So11Deo6loria/bhvBadge2023/hardware/Badgetastic/Badgetastic.kicad_pcb

## KiCad design aqua_pcb/breakout_board.kicad_pcb

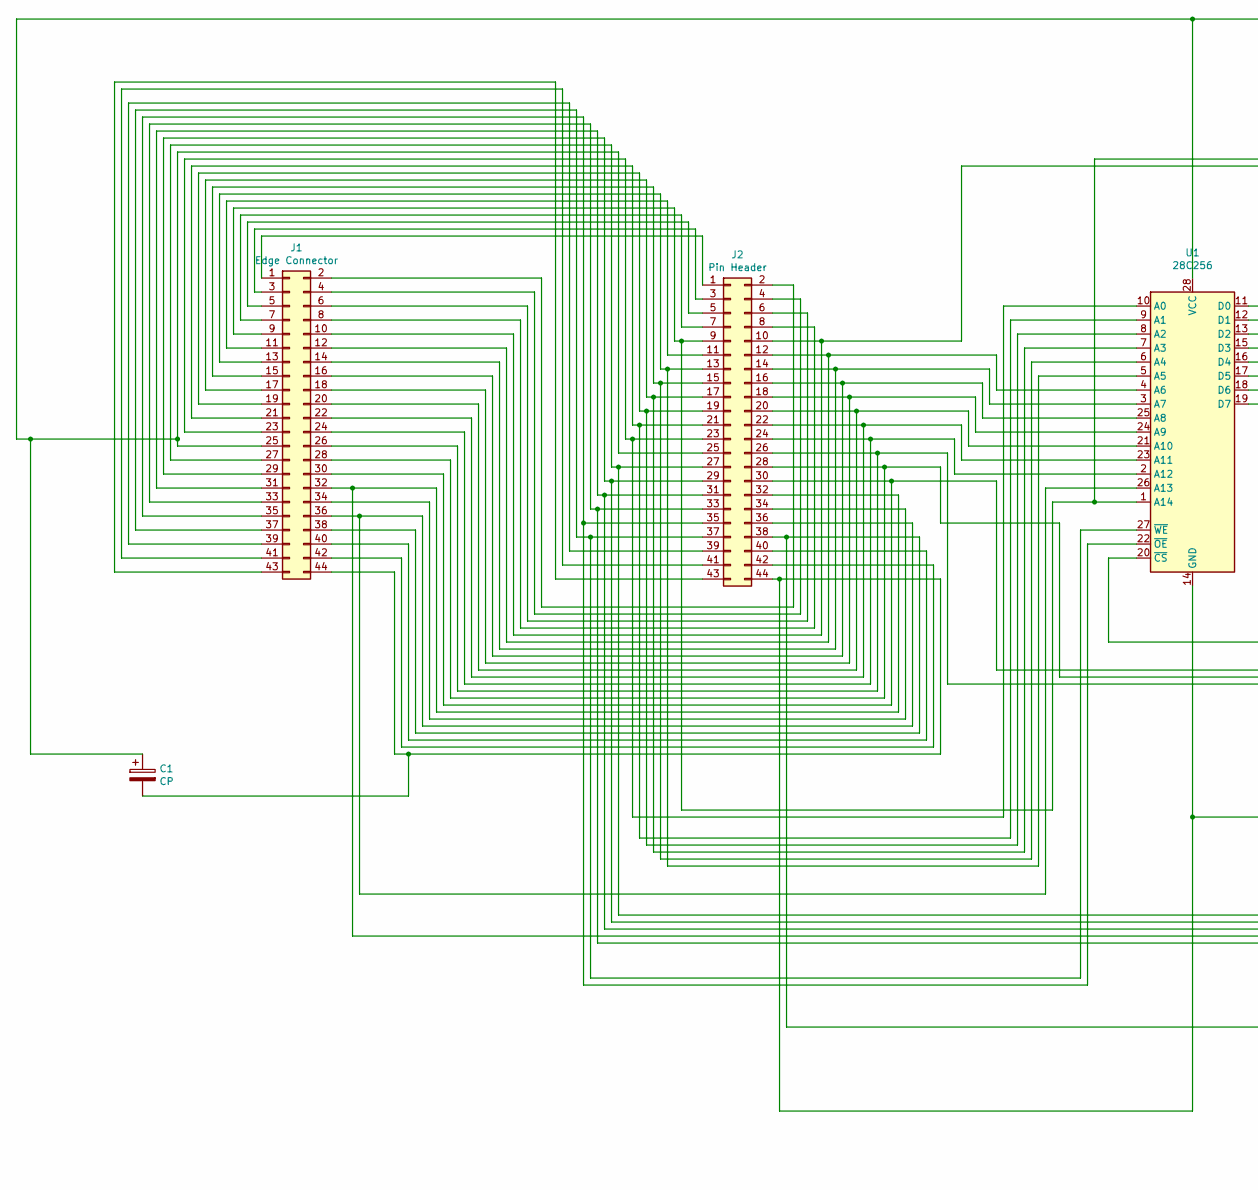
[picture p2: schematic breakout_board.sch, part in row 1, column 1]

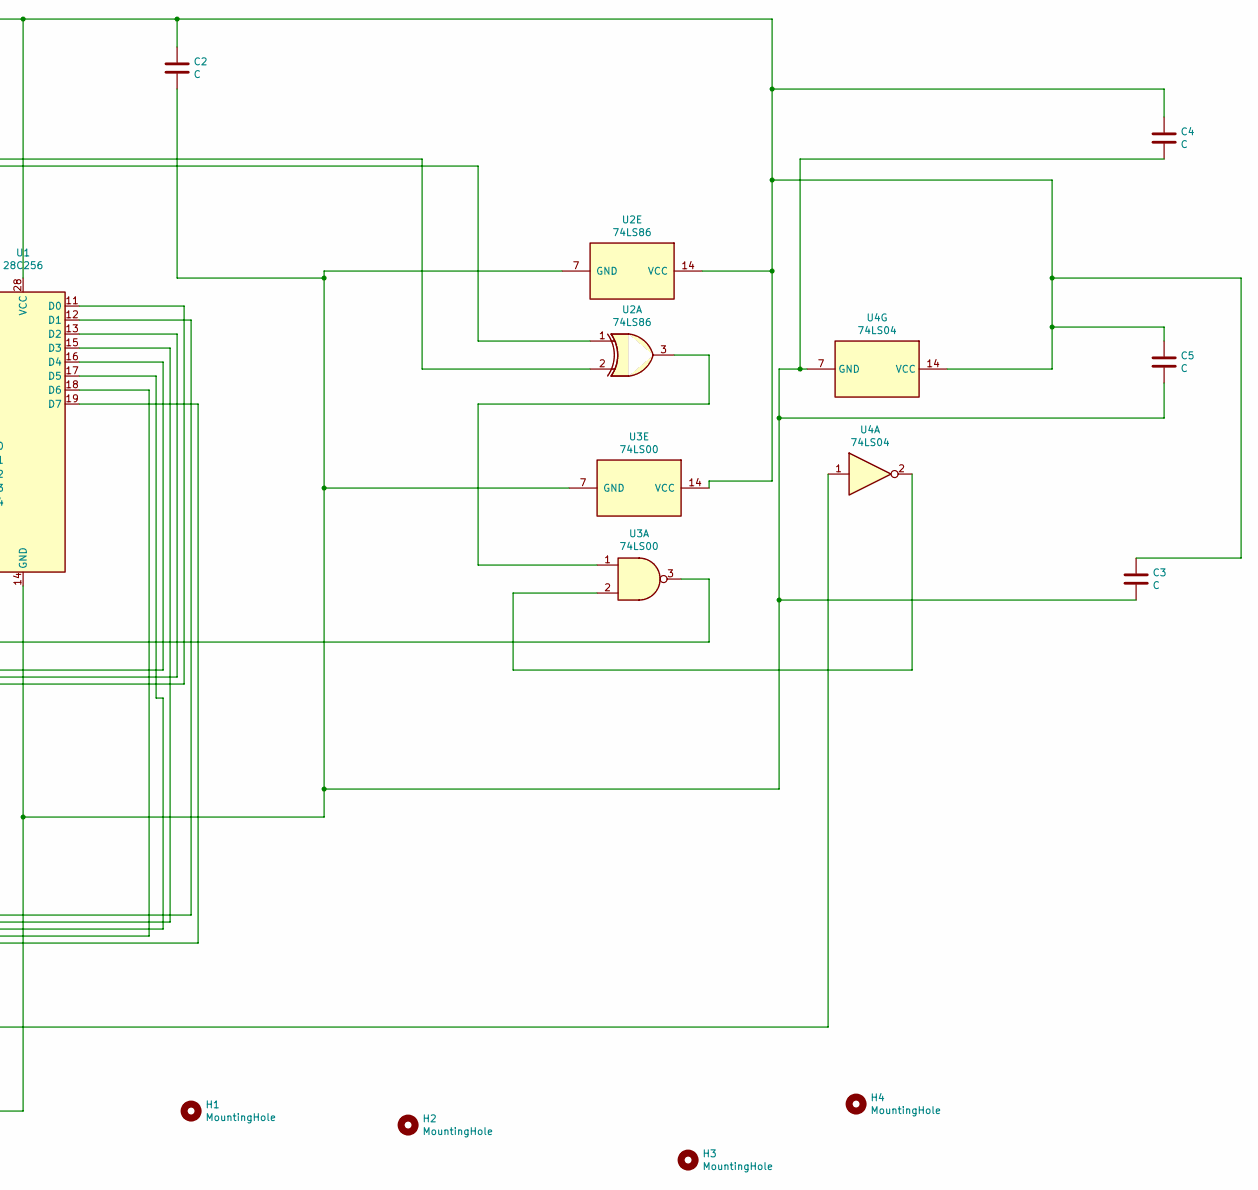
[picture p3: schematic breakout_board.sch, part in row 1, column 2]

Parts:
C1: CP; CP_Radial_D14.0mm_P7.50mm
C2, C3, C4, C5: C; C_Disc_D4.3mm_W1.9mm_P5.00mm
H1, H2, H3, H4: MountingHole; MountingHole_3.2mm_M3
J1: Edge Connector; Aquarius_Cartridge
J2: Pin Header; PinSocket_2x22_P2.54mm_Vertical
U1: 28C256; DIP-28_W15.24mm
U2: 74LS86; DIP-14_W7.62mm
U3: 74LS00; DIP-14_W7.62mm
U4: 74LS04; DIP-14_W7.62mm

Connections:
unnamed: C1.1, C2.1, C3.1, C4.1, C5.1, J1.25, J2.25, U1.28 (VCC), U2.14 (VCC), U3.14 (VCC), U4.14 (VCC)
unnamed: C1.2, C2.2, C3.2, C4.2, C5.2, J1.44, J2.44, U1.14 (GND), U2.7 (GND), U3.7 (GND), U4.7 (GND)
unnamed: J1.1, J2.1
unnamed: J1.2, J2.2
unnamed: J1.3, J2.3
unnamed: J1.4, J2.4
unnamed: J1.5, J2.5
unnamed: J1.6, J2.6
unnamed: J1.7, J2.7
unnamed: J1.8, J2.8
unnamed: J1.9, J2.9, U1.1 (A14), U2.2
unnamed: J1.10, J2.10, U2.1
unnamed: J1.11, J2.11
unnamed: J1.12, J2.12, U1.4 (A6)
unnamed: J1.13, J2.13, U1.5 (A5)
unnamed: J1.14, J2.14, U1.3 (A7)
unnamed: J1.15, J2.15, U1.6 (A4)
unnamed: J1.16, J2.16, U1.25 (A8)
unnamed: J1.17, J2.17, U1.7 (A3)
unnamed: J1.18, J2.18, U1.24 (A9)
unnamed: J1.19, J2.19, U1.8 (A2)
unnamed: J1.20, J2.20, U1.21 (A10)
unnamed: J1.21, J2.21, U1.9 (A1)
unnamed: J1.22, J2.22, U1.23 (A11)
unnamed: J1.23, J2.23, U1.10 (A0)
unnamed: J1.24, J2.24, U1.2 (A12)
unnamed: J1.26, J2.26, U1.11 (D0)
unnamed: J1.27, J2.27, U1.12 (D1)
unnamed: J1.28, J2.28, U1.13 (D2)
unnamed: J1.29, J2.29, U1.15 (D3)
unnamed: J1.30, J2.30, U1.16 (D4)
unnamed: J1.31, J2.31, U1.17 (D5)
unnamed: J1.32, J2.32, U1.18 (D6)
unnamed: J1.33, J2.33, U1.19 (D7)
unnamed: J1.34, J2.34
unnamed: J1.35, J2.35, U1.22 (~OE)
unnamed: J1.36, J2.36, U1.26 (A13)
unnamed: J1.37, J2.37, U1.27 (~WE)
unnamed: J1.38, J2.38, U4.1
unnamed: J1.39, J2.39
unnamed: J1.40, J2.40
unnamed: J1.41, J2.41
unnamed: J1.42, J2.42
unnamed: J1.43, J2.43
unnamed: U1.20 (~CS), U3.3
unnamed: U2.3, U3.1
unnamed: U3.2, U4.2

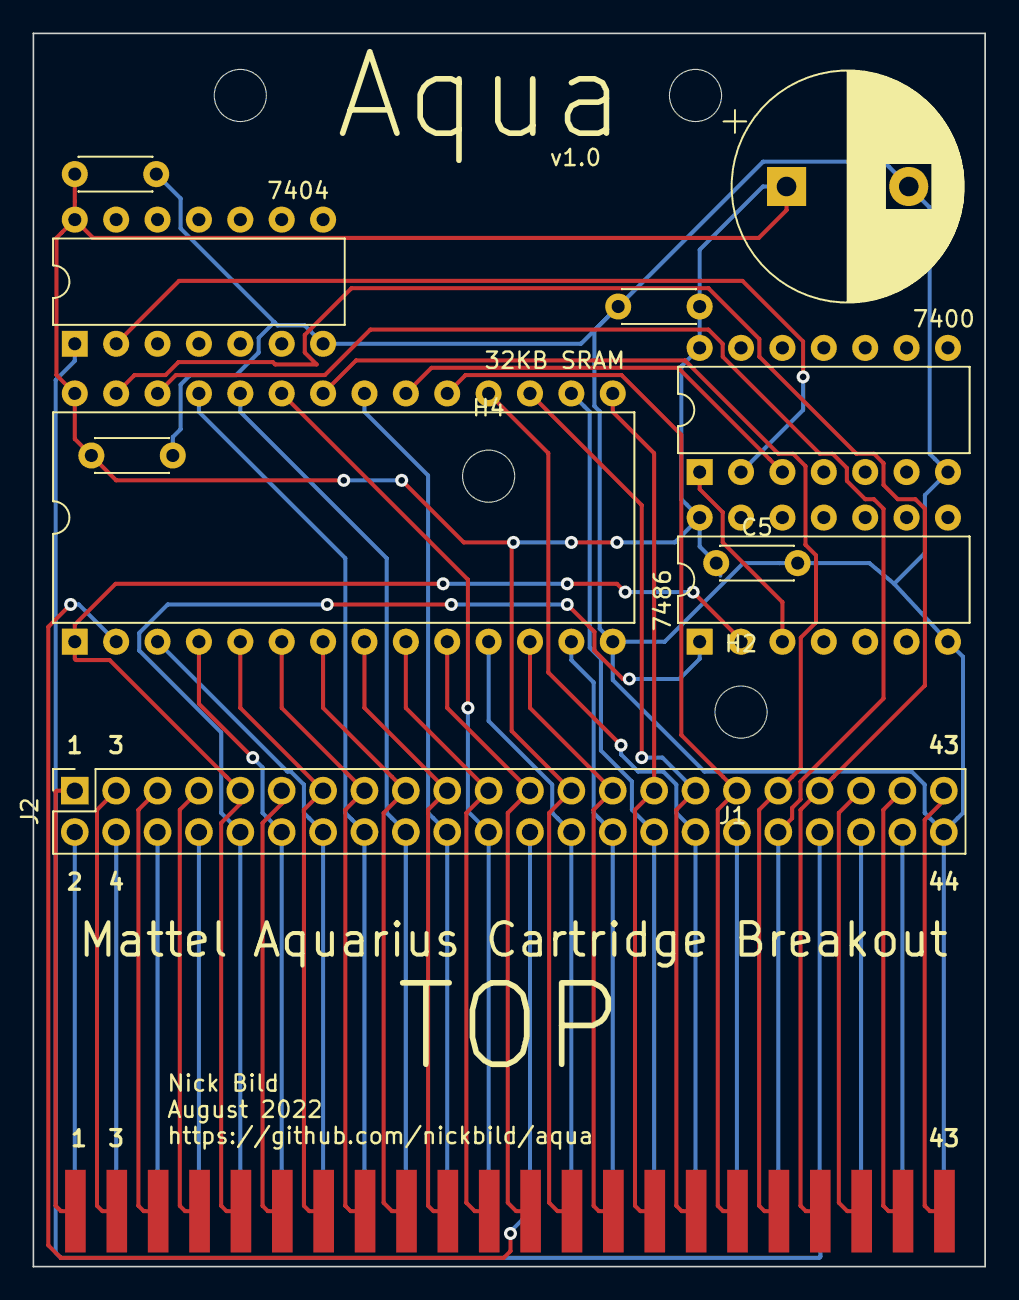
[picture p4: board breakout_board.kicad_pcb from above]

Board: 2 copper layers, 58.4 x 75.7 mm, 15 parts (0 on the bottom side), 47 nets.
