So11Deo6loria/bhvBadge2023/scripts/chart.py

#!/usr/bin/python3

import matplotlib.pyplot as plt

#I haven't found a better way to plot the data off of the pico

#So I am manually copying and pasting the irvalues and time values from the chart files that are generated on the pico
irVal = {"0": 2817, "1": 2817, "2": 2818, "3": 2818, "4": 2818, "5": 2819, "6": 2819, "7": 2819, "8": 2820, "9": 2820, "10": 2821, "11": 2821, "12": 2822, "13": 2822, "14": 2823, "15": 2823, "16": 2824, "17": 2824, "18": 2824, "19": 2825, "20": 2826, "21": 2826, "22": 2826, "23": 2827, "24": 2827, "25": 2828, "26": 2829, "27": 2829, "28": 2830, "29": 2830, "30": 2831, "31": 2832, "32": 2832, "33": 2832, "34": 2833, "35": 2833, "36": 2832, "37": 2833, "38": 2832, "39": 2832, "40": 2831, "41": 2831, "42": 2831, "43": 2831, "44": 2830, "45": 2830, "46": 2829, "47": 2829, "48": 2829, "49": 2829, "50": 2828, "51": 2828, "52": 2828, "53": 2829, "54": 2829, "55": 2829, "56": 2829, "57": 2829, "58": 2830, "59": 2830, "60": 2830, "61": 2830, "62": 2830, "63": 2830, "64": 2831, "65": 2831, "66": 2832, "67": 2832, "68": 2832, "69": 2833, "70": 2833, "71": 2833, "72": 2832, "73": 2832, "74": 2833, "75": 2832, "76": 2833, "77": 2833, "78": 2834, "79": 2834, "80": 2834, "81": 2835, "82": 2835, "83": 2834, "84": 2834, "85": 2834, "86": 2835, "87": 2835, "88": 2836, "89": 2836, "90": 2836, "91": 2836, "92": 2837, "93": 2837, "94": 2837, "95": 2837, "96": 2837, "97": 2837, "98": 2838, "99": 2838, "100": 2838, "101": 2839, "102": 2839, "103": 2839, "104": 2839, "105": 2840, "106": 2840, "107": 2841, "108": 2840, "109": 2840, "110": 2840, "111": 2840, "112": 2840, "113": 2840, "114": 2839, "115": 2840, "116": 2840, "117": 2841, "118": 2841, "119": 2841, "120": 2840, "121": 2841, "122": 2842, "1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
#x = list(timeVal.values()) #uncomment this line to use the the timevaleus as the x axis

y = list(irVal.values())

plt.plot(x, y)
plt.xlabel('Time (ms)')
plt.ylabel('IR Value')
plt.title('Plot of the read IR Values ' + str(len(irVal)) + ' samples')
plt.show()
